naKoleniNaGitu/myAntWeightBot/pictures/500px-ESP32-S3-Zero_02.jpg

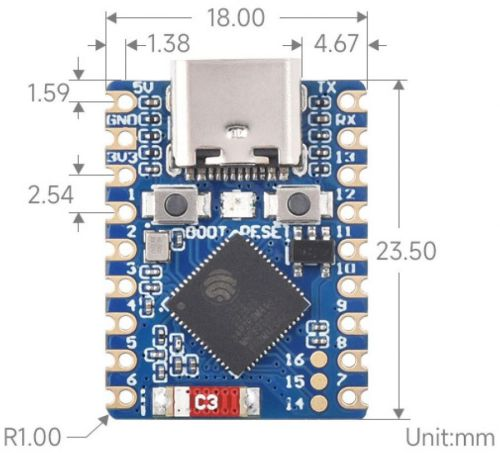
pictures/500px-ESP32-S3-Zero_02.jpg
