naKoleniNaGitu/myAntWeightBot/pictures/blade2.png

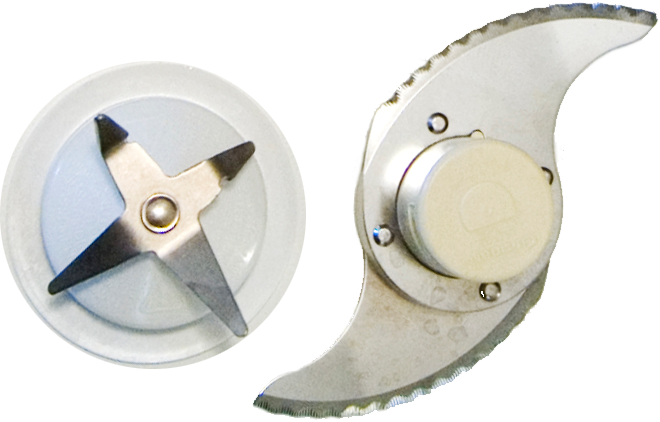
pictures/blade2.png
