naKoleniNaGitu/myAntWeightBot/pictures/blade.webp

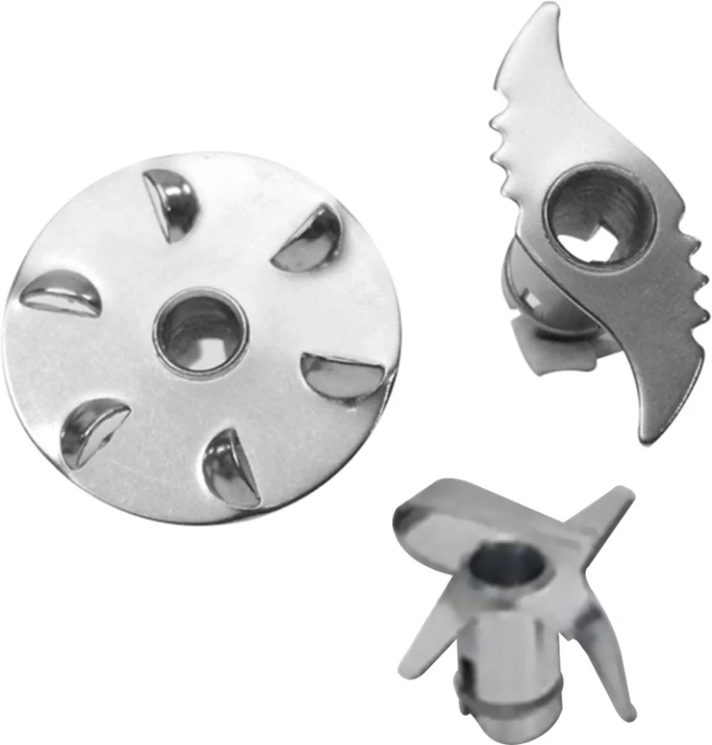
pictures/blade.webp
