naKoleniNaGitu/myAntWeightBot/pictures/deathroll.jpeg

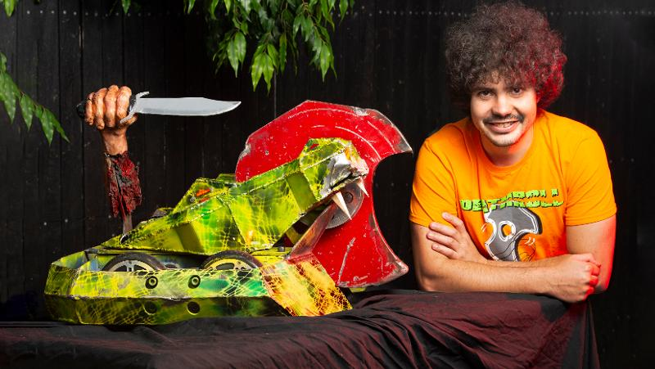
pictures/deathroll.jpeg
