naKoleniNaGitu/myAntWeightBot/pictures/first outline.jpg

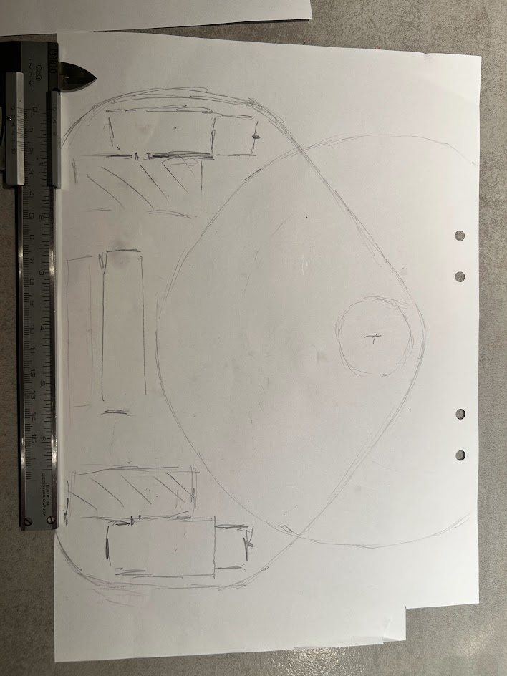
pictures/first outline.jpg
