naKoleniNaGitu/myAntWeightBot/pictures/strawberry.jpg

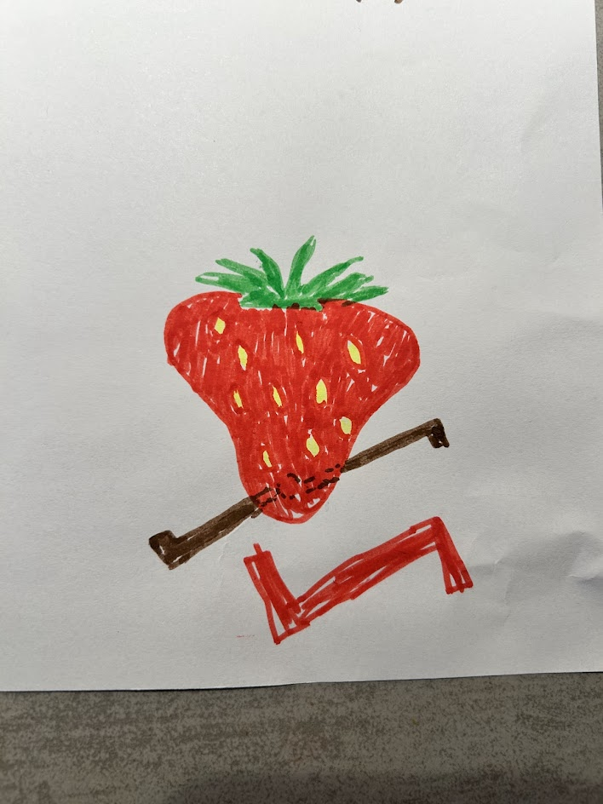
pictures/strawberry.jpg
