naKoleniNaGitu/myAntWeightBot/pictures/ufo.jpg

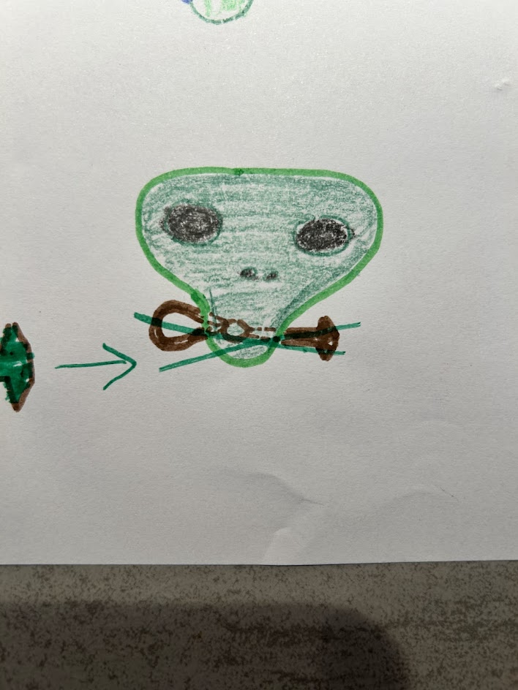
pictures/ufo.jpg
