naKoleniNaGitu/myAntWeightBot/STL/BearingHolder v21.stl

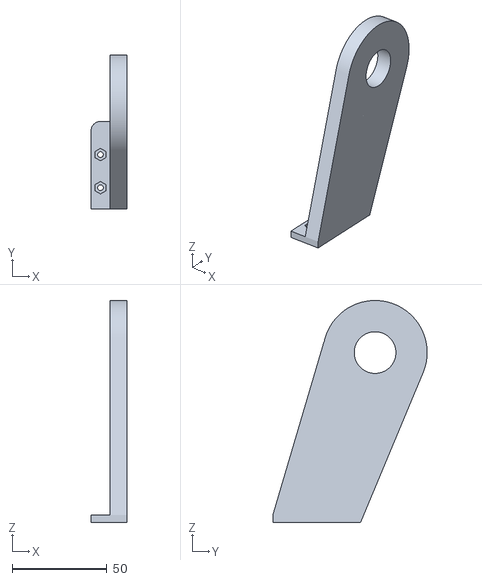
[picture p34: CAD file, 2025-11-14]
STL/BearingHolder v21.stl
19.0 x 81.5 x 117.2
