naKoleniNaGitu/myAntWeightBot/STL/SlidingPad 3 v15.stl

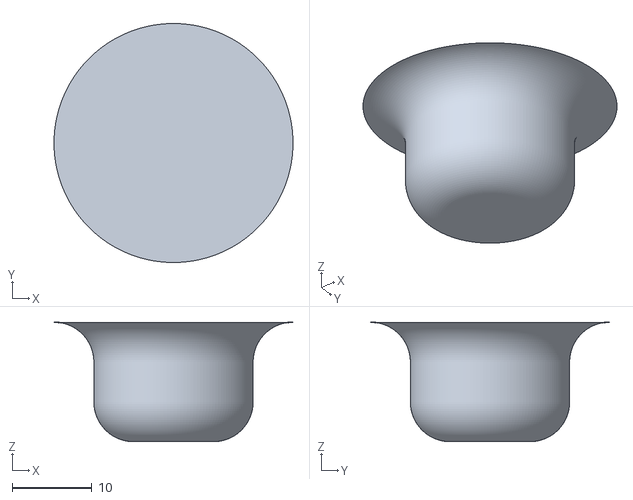
[picture p35: CAD file, 2025-11-14]
STL/SlidingPad 3 v15.stl
30.0 x 30.0 x 15.0
