naKoleniNaGitu/myAntWeightBot/STL/BasePlate.stl

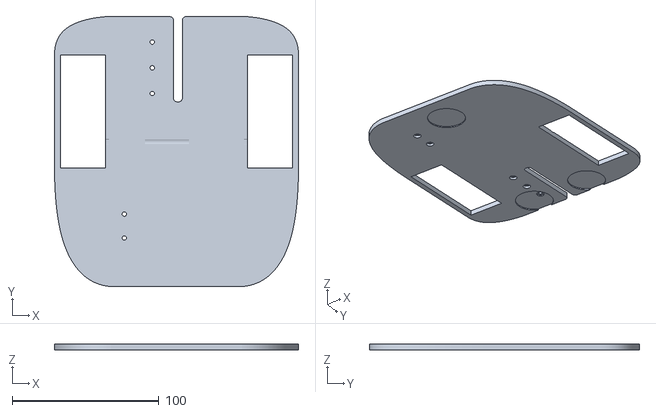
[picture p36: CAD file, 2025-11-14]
STL/BasePlate.stl
166.1 x 183.9 x 4.00
