naKoleniNaGitu/myAntWeightBot/STL/Armor v32.stl

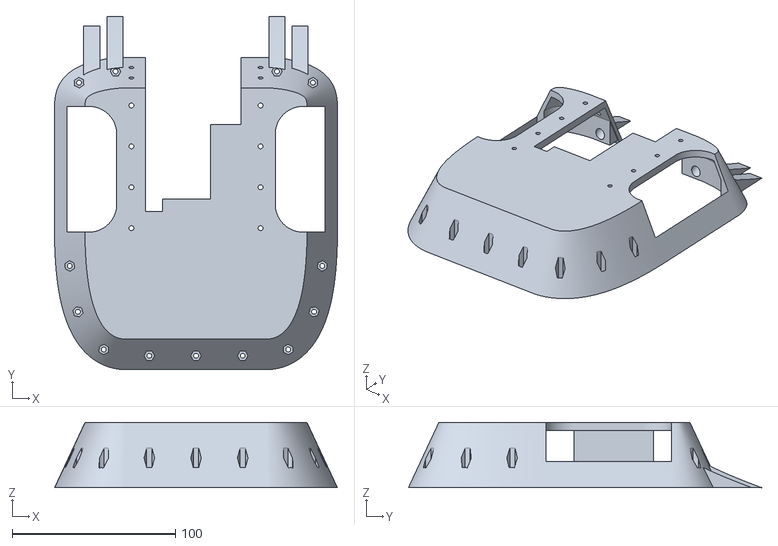
[picture p37: CAD file, 2025-11-14]
STL/Armor v32.stl
173.1 x 216.1 x 40.0
