naKoleniNaGitu/myAntWeightBot/STL/Shell v31.stl

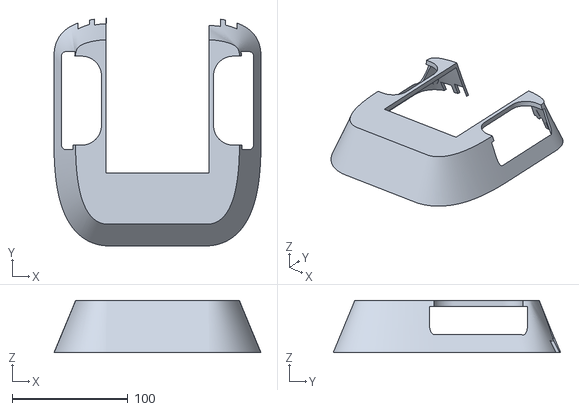
[picture p38: CAD file, 2025-11-14]
STL/Shell v31.stl
179.1 x 196.9 x 45.0
