naKoleniNaGitu/myAntWeightBot/STL/BladeHolder v15.stl

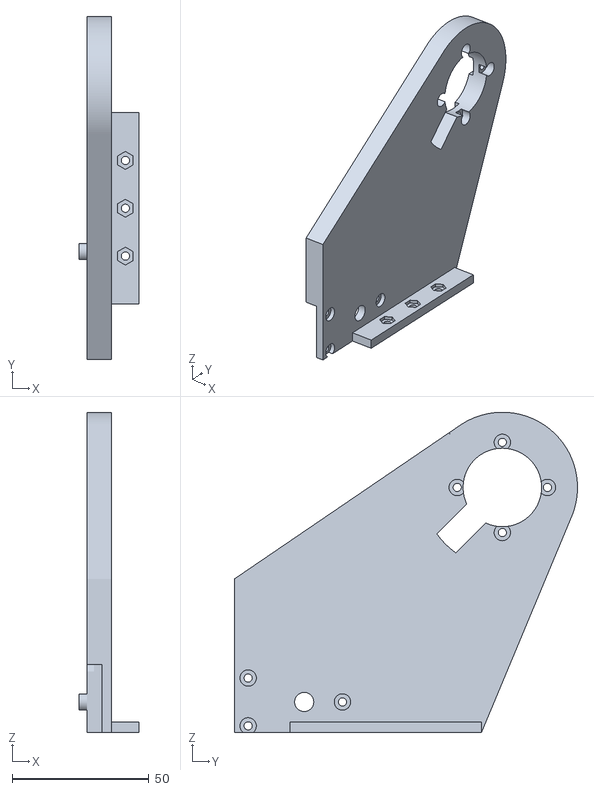
[picture p39: CAD file, 2025-11-14]
STL/BladeHolder v15.stl
22.0 x 125.5 x 117.2
