naKoleniNaGitu/myAntWeightBot/STL/AMASS_XT60-M_1x02_P7.2mm_Vertical v2.step

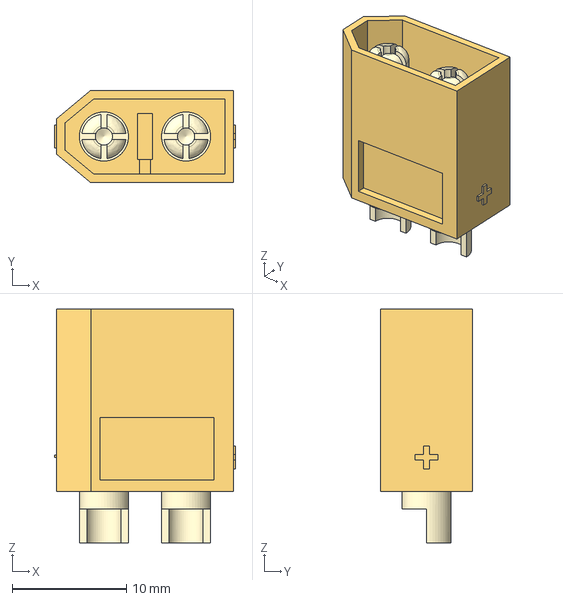
[picture p40: CAD file, 2025-11-14]
STL/AMASS_XT60-M_1x02_P7.2mm_Vertical v2.step
15.9 x 8.10 x 20.5 mm
