naKoleniNaGitu/myAntWeightBot/STL/Shim v31.stl

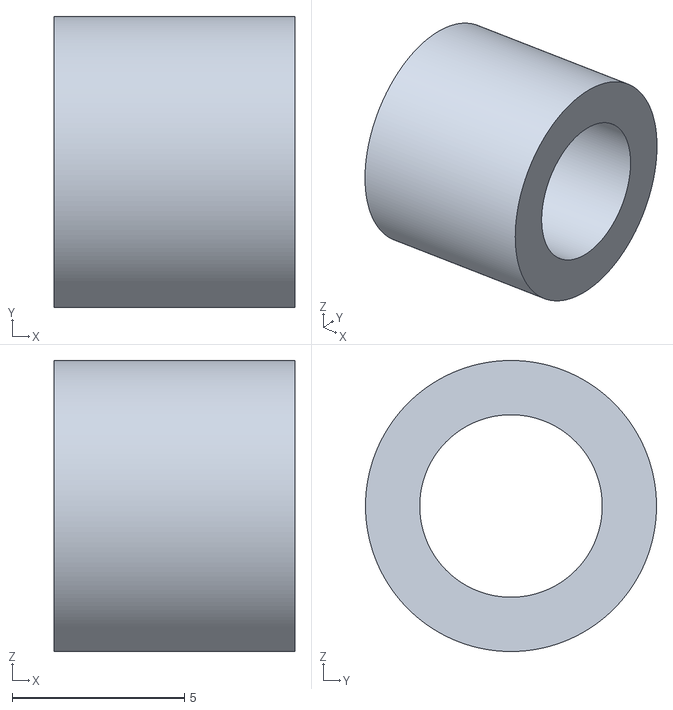
[picture p41: CAD file, 2025-11-14]
STL/Shim v31.stl
7.00 x 8.45 x 8.45
