naKoleniNaGitu/myAntWeightBot/platformio_projects/myAntWeightBot_v3/components/arduino/docs/_static/external_library_test_schedule.png

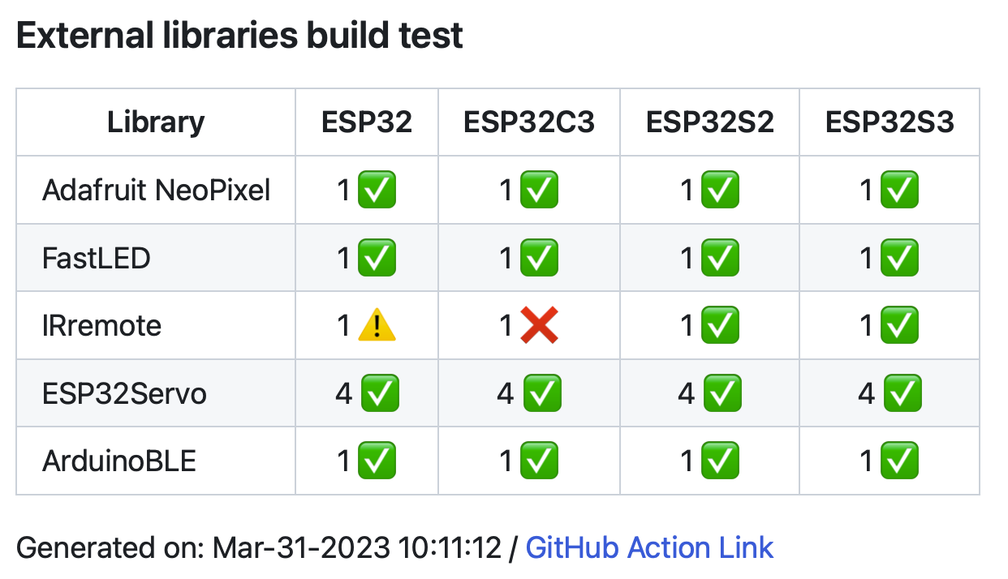
platformio_projects/myAntWeightBot_v3/components/arduino/docs/_static/external_library_test_schedule.png
