naKoleniNaGitu/myAntWeightBot/voltage measurement.jpeg

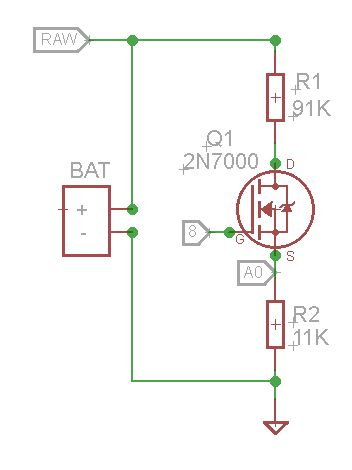
voltage measurement.jpeg
