naKoleniNaGitu/myAntWeightBot/Arduino Code/TelemetryOLED/TelemetryOLED.ino

// Include the correct display library

// For a connection via I2C using the Arduino Wire include:
#include <Wire.h>               // Only needed for Arduino 1.6.5 and earlier
#include "SSD1306Wire.h"        // legacy: #include "SSD1306.h"



// Initialize the OLED display using Arduino Wire:
SSD1306Wire display(0x3c, 2, 1);   // ADDRESS, SDA, SCL  -  SDA and SCL usually populate automatically based on your board's pins_arduino.h e.g. https://github.com/esp8266/Arduino/blob/master/variants/nodemcu/pins_arduino.h

void setup() {
  Serial.begin(115200);
  Serial.println();
  Serial.println();


  // Initialising the UI will init the display too.
  display.init();

  display.flipScreenVertically();
  display.setFont(ArialMT_Plain_10);

}

void simpleTextDemo() {
  display.setTextAlignment(TEXT_ALIGN_LEFT);
  display.setFont(ArialMT_Plain_24);
  display.drawString(0, 0, "SSB: NC");
  display.drawString(0, 25, "UFO: NC");
}




void loop() {
  // clear the display
  display.clear();
  // draw the current demo method

  simpleTextDemo();
  
  // ms time print
  display.setFont(ArialMT_Plain_10);
  display.setTextAlignment(TEXT_ALIGN_RIGHT);
  display.drawString(50, 54, String(millis()));
  // write the buffer to the display
  display.display();

  delay(10);
}
